L0czek/ircc/controller/src/ctl.cc

#include <cstdio>
#include <expected>
#include <memory>

#include "ctl.h"

#include "board.h"
#include "message_handler.hpp"
#include "charger.hpp"
#include "output_voltage_regulator.hpp"
#include "dac_controller.hpp"
#include "cmsis_os2.h"
#include "config.hpp"
#include "log.hpp"
#include "stm32g4xx_hal_uart.h"
#include "stm32g4xx_hal_uart_ex.h"
#include "thread.hpp"

board_config BOARD_CONFIG;
MessageHandler message_handler;
Charger* charger = nullptr;
OutputVoltageRegulator* output_voltage_regulator = nullptr;
DACController* dac_controller = nullptr;


extern "C" void controller_system_init(const board_config *config) {
    BOARD_CONFIG = *config;

    // Initialize charger with I2C handle from board config
    charger = new Charger(BOARD_CONFIG.i2c);
    if (!charger->initialize()) {
        os::error("Failed to initialize charger\n");
    }

    // Initialize output voltage regulator with I2C handle from board config
    output_voltage_regulator = new OutputVoltageRegulator(BOARD_CONFIG.i2c);
    if (!output_voltage_regulator->initialize()) {
        os::error("Failed to initialize output voltage regulator\n");
    }

    // Initialize DAC controller with DAC handles from board config
    dac_controller = new DACController(BOARD_CONFIG.dac);
    if (!dac_controller->initialize()) {
        os::error("Failed to initialize DAC controller\n");
    }

    os::init(os::LogLevel::Debug);
    os::info("Booting up\n");

    static osThreadAttr_t message_handler_sender_thread_attr = {
        .name = "message-handler-sender-thread",
        .attr_bits = osThreadDetached,
        .cb_mem = nullptr,
        .cb_size = 0,
        .stack_mem = nullptr,
        .stack_size = 0,
        .priority = osPriorityNormal,
        .tz_module = 0,
        .reserved = 0
    };

    static auto message_handler_sender_thread = os::thread(
        &message_handler_sender_thread_attr,
        &MessageHandler::run_sender,
        std::move(&message_handler)
    );

    static osThreadAttr_t message_handler_receiver_thread_attr = {
        .name = "message-handler-receiver-thread",
        .attr_bits = osThreadDetached,
        .cb_mem = nullptr,
        .cb_size = 0,
        .stack_mem = nullptr,
        .stack_size = 0,
        .priority = osPriorityNormal1,
        .tz_module = 0,
        .reserved = 0
    };

    static auto message_handler_receiver_thread = os::thread(
        &message_handler_receiver_thread_attr,
        &MessageHandler::run_receiver,
        std::move(&message_handler)
    );
}

extern "C" void HAL_UART_TxCpltCallback([[maybe_unused]] UART_HandleTypeDef *huart) {
    message_handler.message_tx_isr();
}

extern "C" void HAL_UARTEx_RxEventCallback(UART_HandleTypeDef *huart, uint16_t ) {
    if (HAL_UARTEx_GetRxEventType(huart) == HAL_UART_RXEVENT_IDLE)
        message_handler.message_rx_isr();
}
